swapsCAPS/esp32-woohoo/images/1.jpg

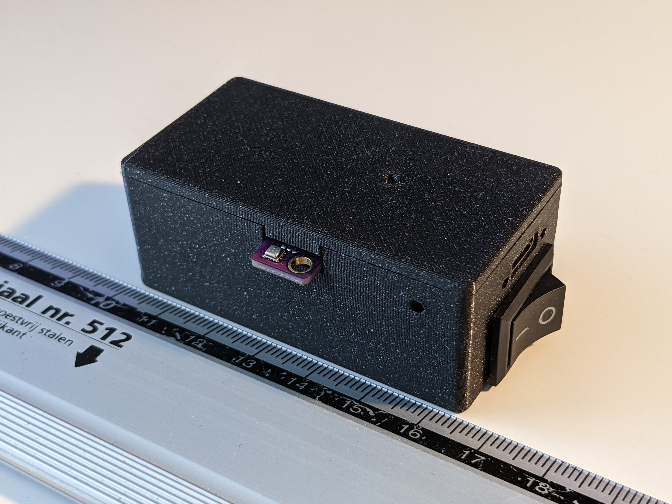
images/1.jpg
