swapsCAPS/esp32-woohoo/images/2.jpg

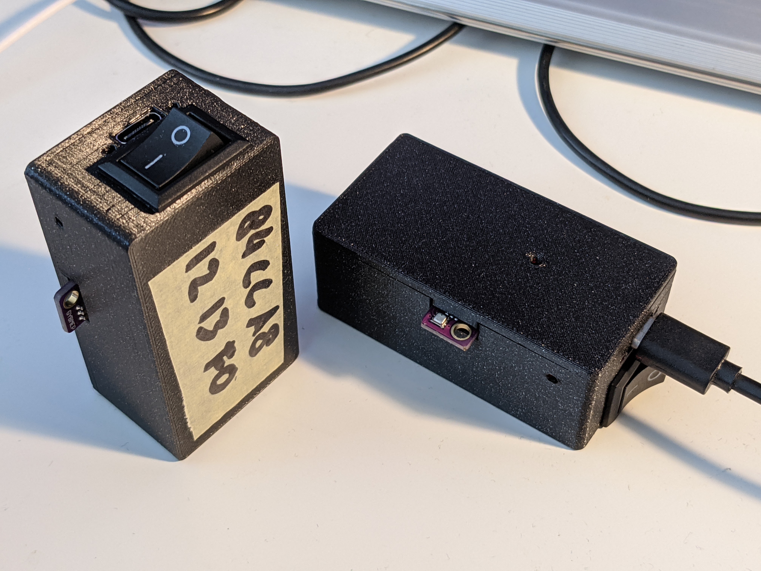
images/2.jpg
